chriswblake/lanyard-tags/designs/rocket/insert-red.stl

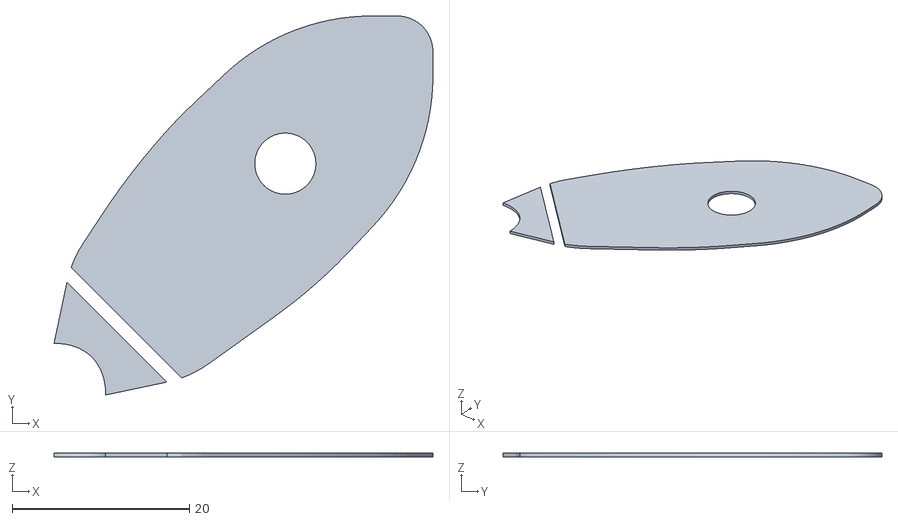
[picture p22: CAD file, 2024-10-22]
designs/rocket/insert-red.stl
42.7 x 42.7 x 0.4
