chriswblake/lanyard-tags/designs/hello-kitty/hello-kitty.3mf

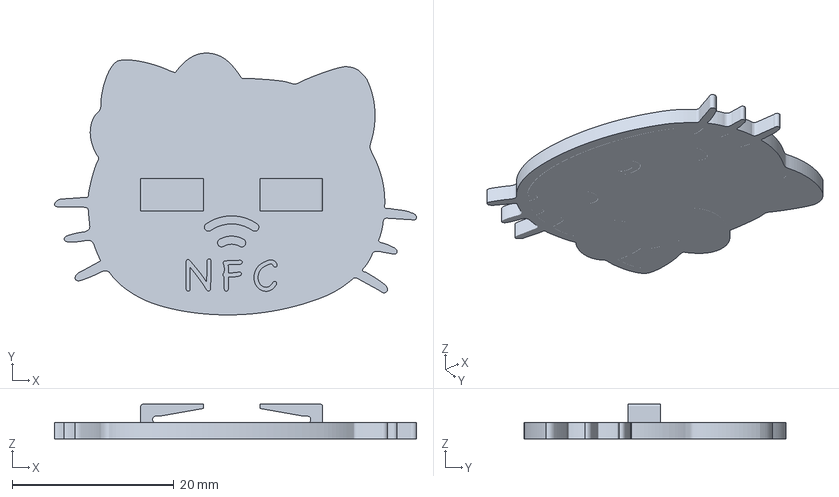
[picture p23: CAD file, 2024-10-22]
designs/hello-kitty/hello-kitty.3mf
44.7 x 32.3 x 4.30 mm
