chriswblake/lanyard-tags/designs/rocket/insert-yellow.stl

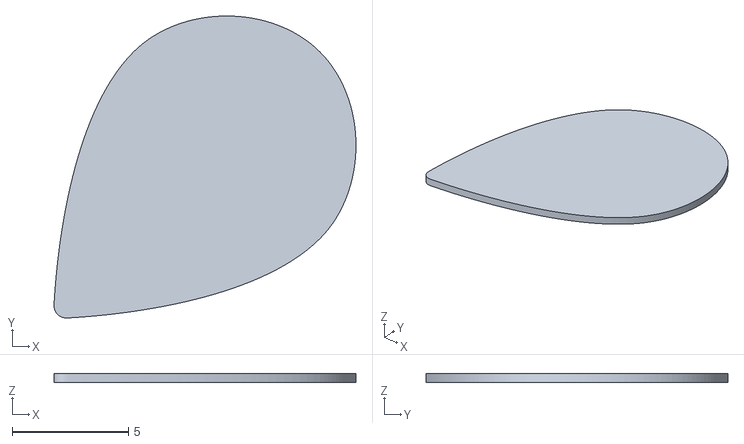
[picture p24: CAD file, 2024-10-22]
designs/rocket/insert-yellow.stl
13.0 x 13.0 x 0.4
