chriswblake/lanyard-tags/designs/hello-kitty/insert-red.stl

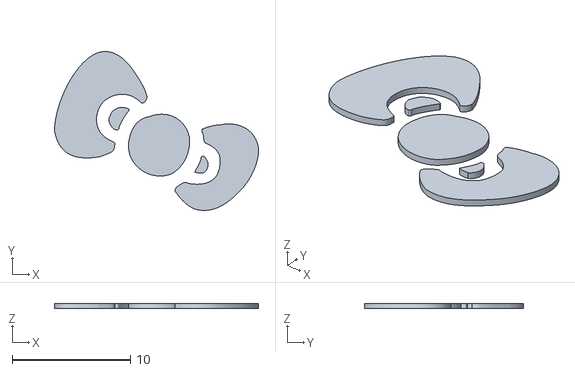
[picture p25: CAD file, 2024-10-22]
designs/hello-kitty/insert-red.stl
17.3 x 13.4 x 0.4
