chriswblake/lanyard-tags/designs/rocket/frame.stl

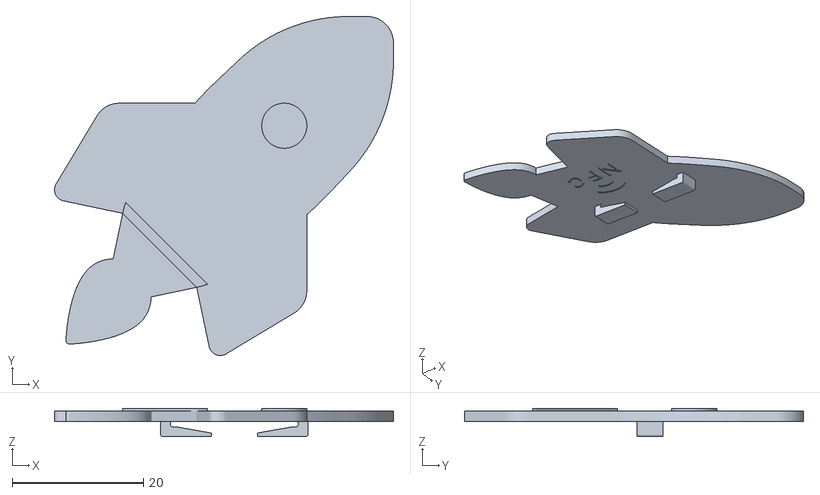
[picture p26: CAD file, 2024-10-22]
designs/rocket/frame.stl
51.7 x 51.7 x 4.30
